gcoonrod/retro-stack/boards/parts/3D/2002101855.stp

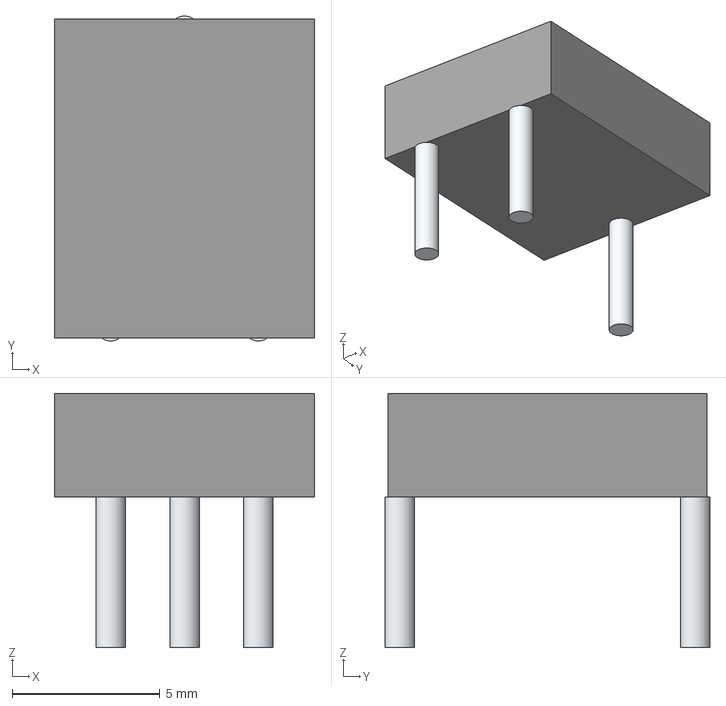
[picture p21: CAD file, 2023-06-14]
boards/parts/3D/2002101855.stp
8.80 x 11.0 x 8.60 mm
Leads
