gcoonrod/retro-stack/boards/parts/3D/532702B02500G.step

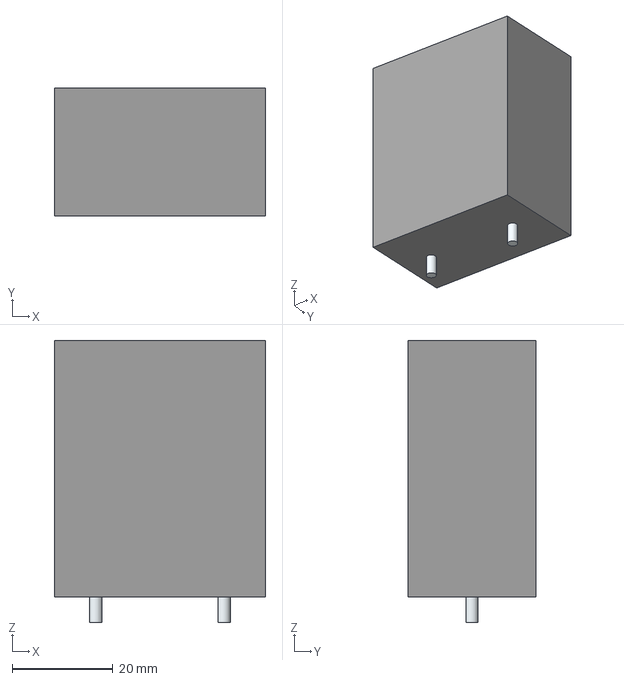
[picture p22: CAD file, 2023-06-14]
boards/parts/3D/532702B02500G.step
41.9 x 25.4 x 55.9 mm
Leads
